TinyTitan/tinytitan.github.io/images/DSC_6004.jpg

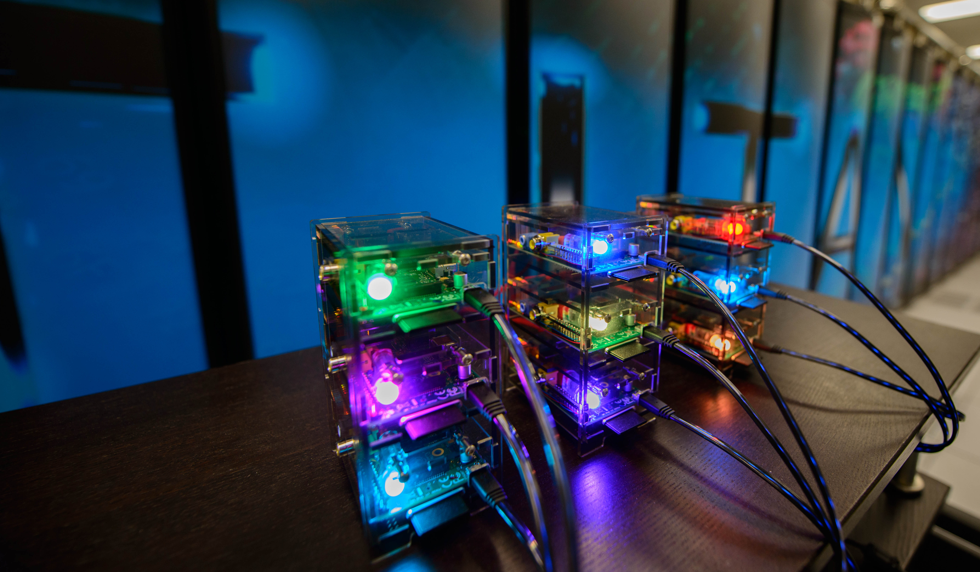
images/DSC_6004.jpg
