TinyTitan/tinytitan.github.io/images/DSC_6060.jpg

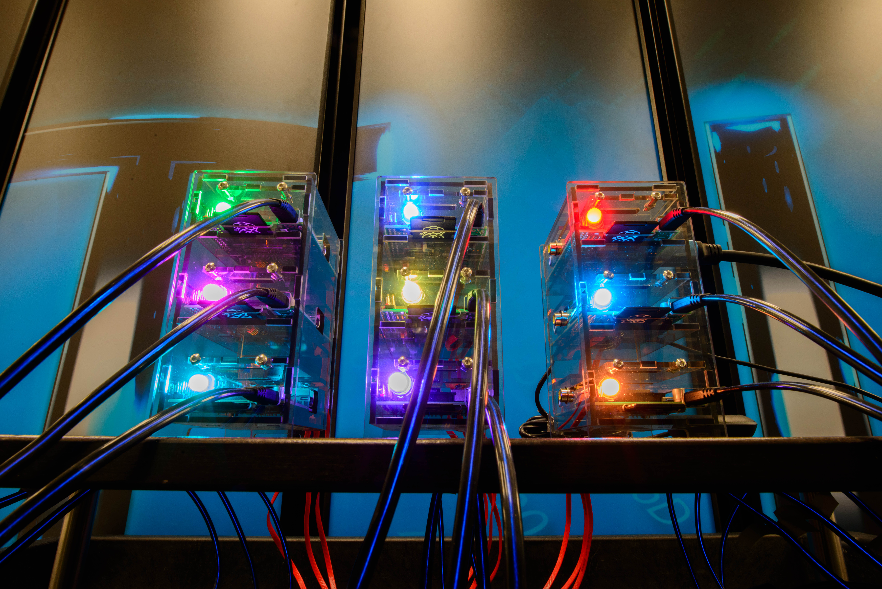
images/DSC_6060.jpg
