TinyTitan/tinytitan.github.io/images/DSC_6062.jpg

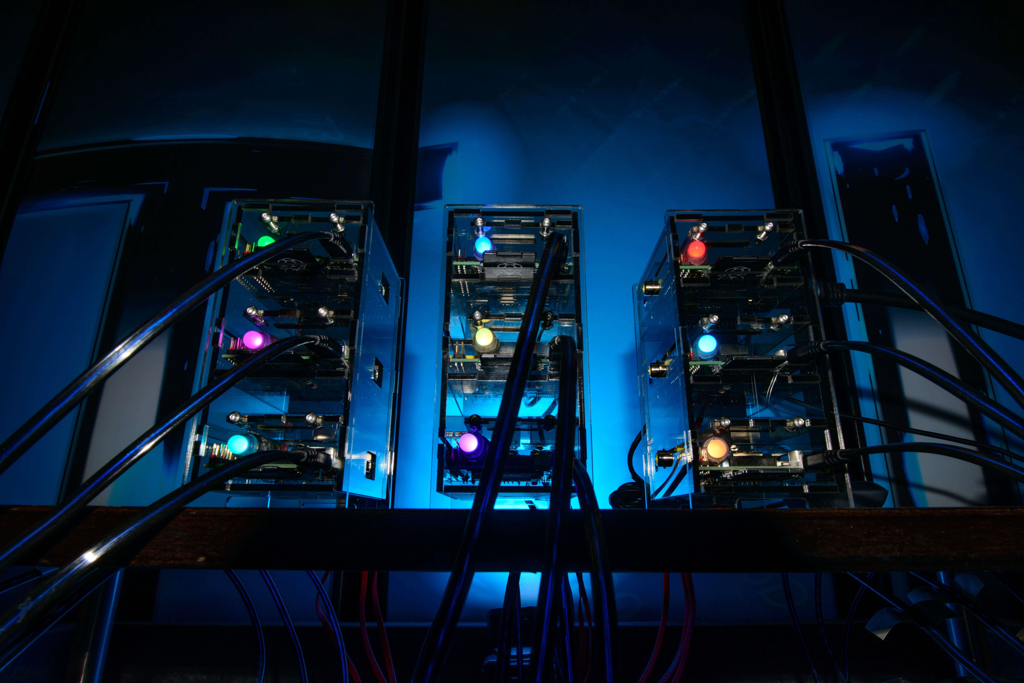
images/DSC_6062.jpg
