TinyTitan/tinytitan.github.io/images/DSC_6087.jpg

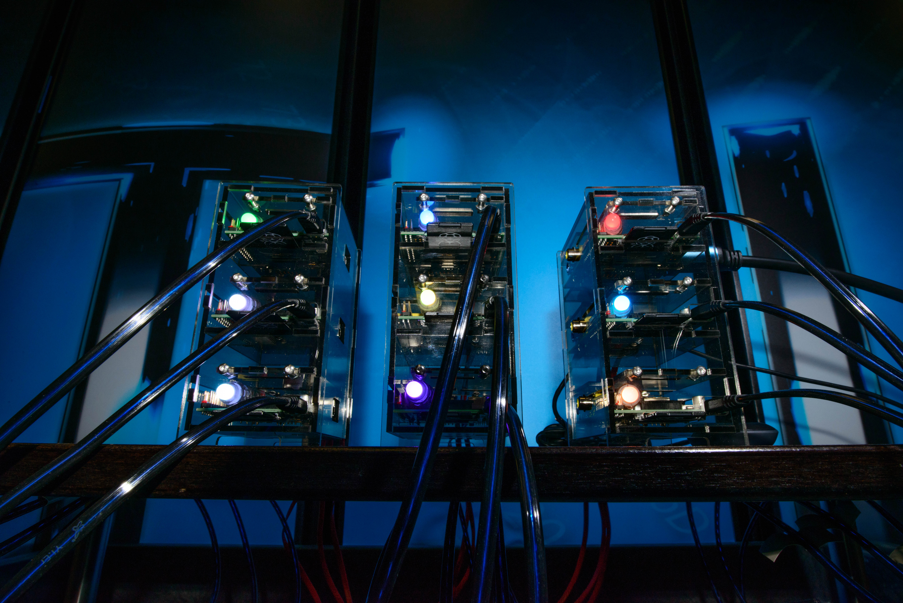
images/DSC_6087.jpg
