TinyTitan/tinytitan.github.io/images/DSC_6102.jpg

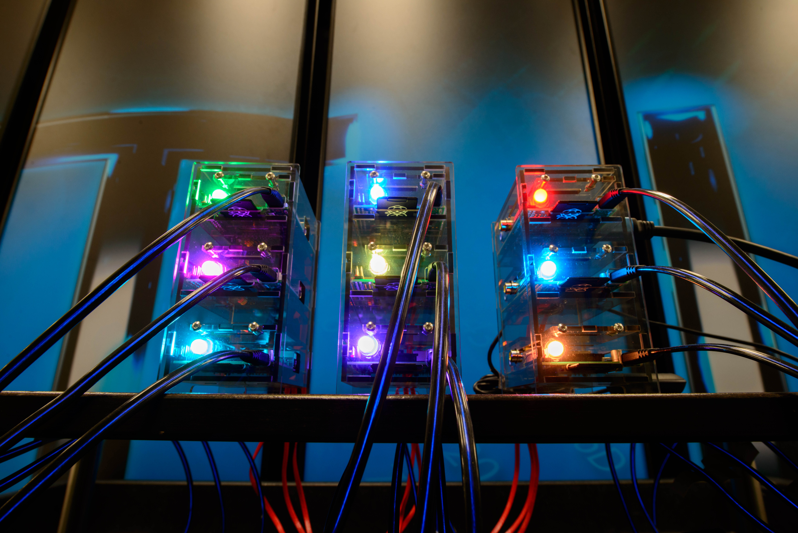
images/DSC_6102.jpg
