TinyTitan/tinytitan.github.io/images/four_cabinet_sph.jpg

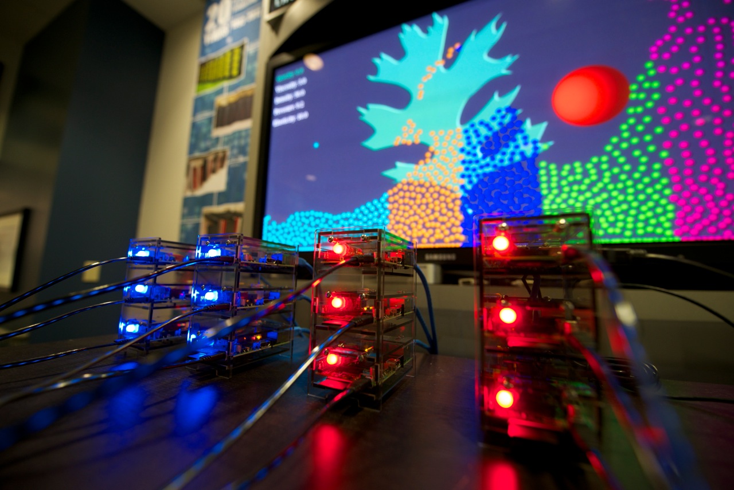
images/four_cabinet_sph.jpg
