TinyTitan/tinytitan.github.io/images/IMG_20140507_095849.jpg

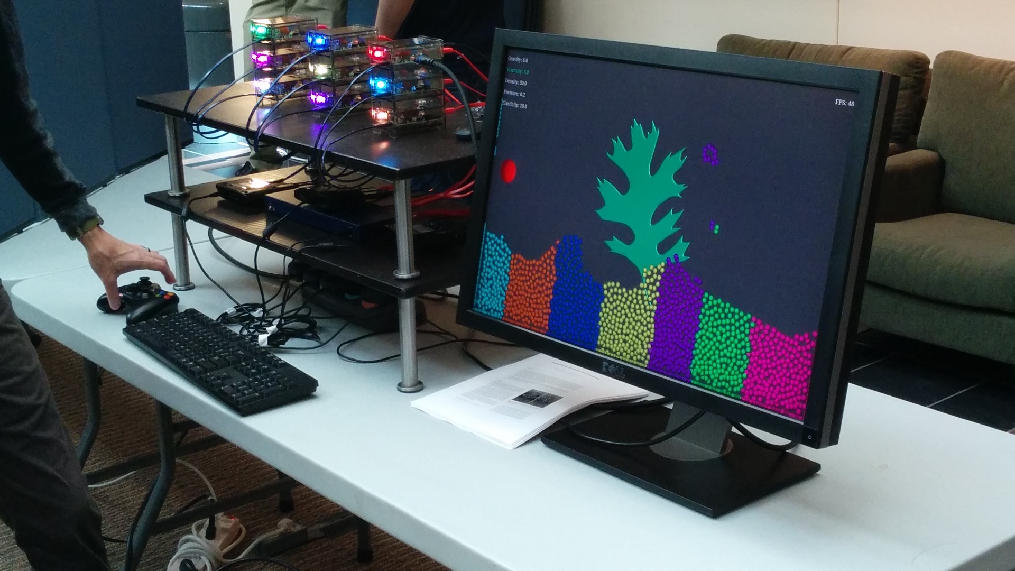
images/IMG_20140507_095849.jpg
