TinyTitan/tinytitan.github.io/images/IMG_20140509_160626.jpg

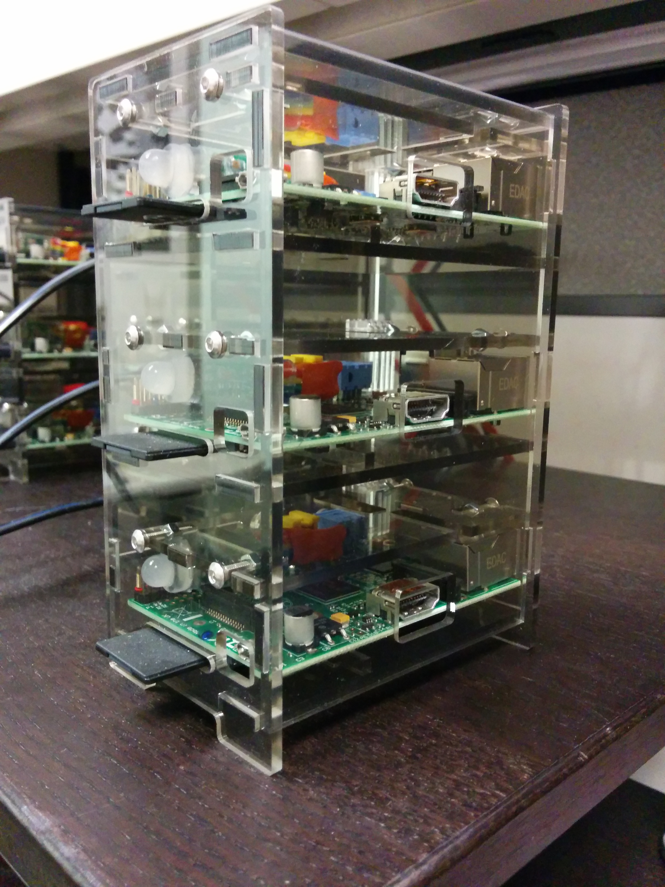
images/IMG_20140509_160626.jpg
