TinyTitan/tinytitan.github.io/images/leaf.png

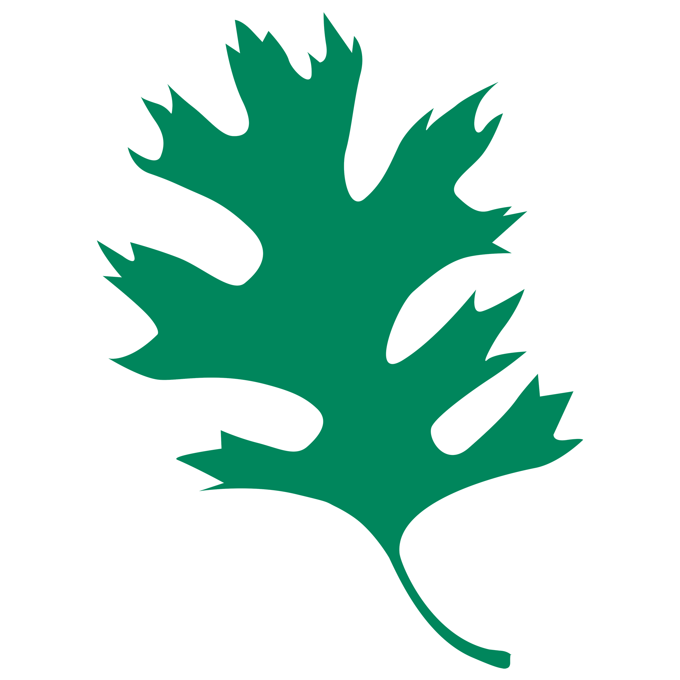
images/leaf.png
