TinyTitan/tinytitan.github.io/images/SPH_Screenshot.png

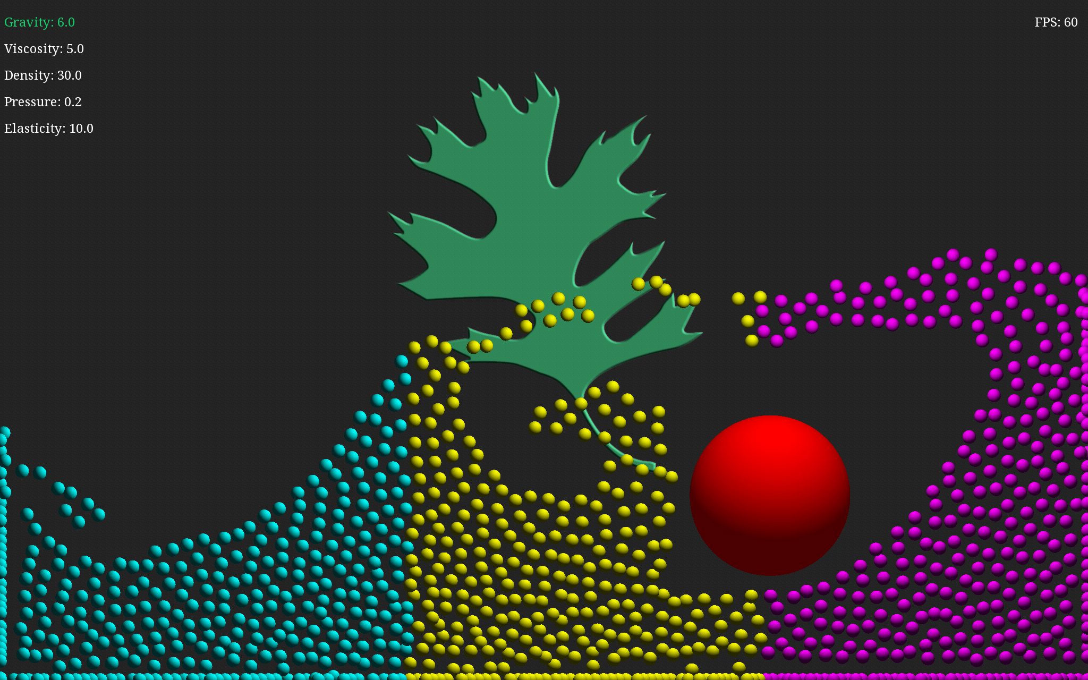
images/SPH_Screenshot.png
