TinyTitan/tinytitan.github.io/images/Construction-v1/image1.jpg

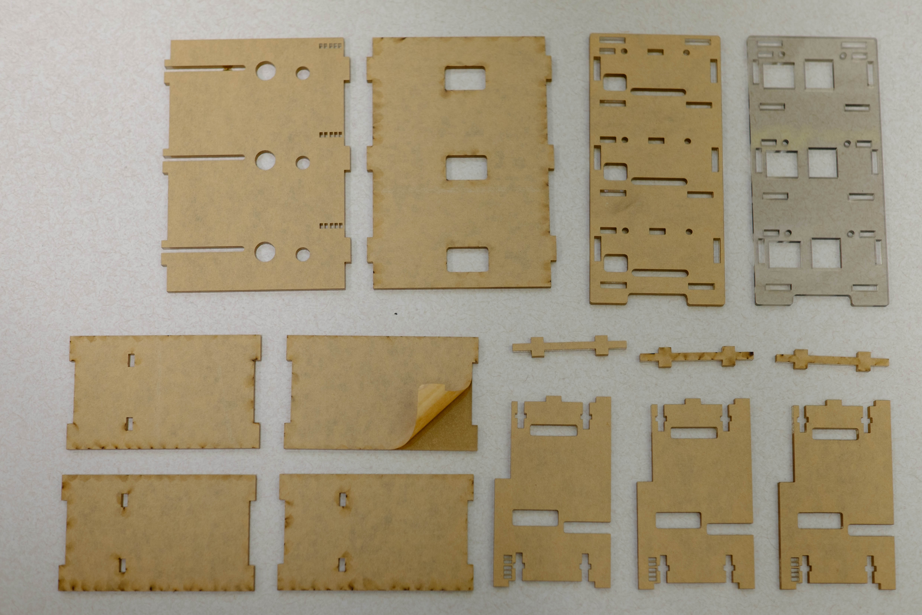
images/Construction-v1/image1.jpg
