TinyTitan/tinytitan.github.io/images/Construction-v1/image2.jpg

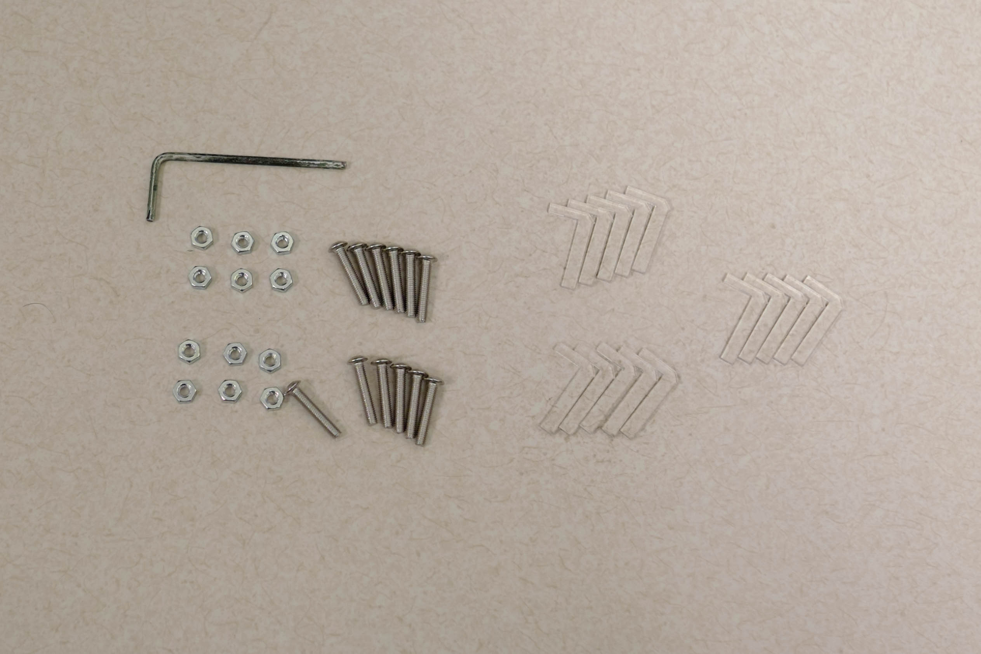
images/Construction-v1/image2.jpg
