TinyTitan/tinytitan.github.io/images/Construction-v1/image3.jpg

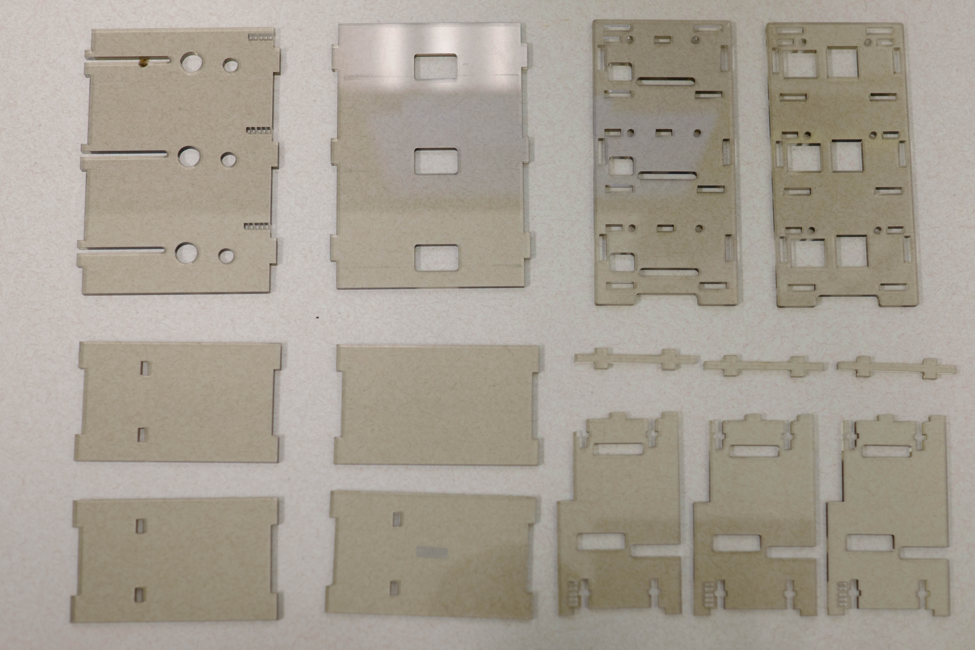
images/Construction-v1/image3.jpg
