TinyTitan/tinytitan.github.io/images/Construction-v1/image4.jpg

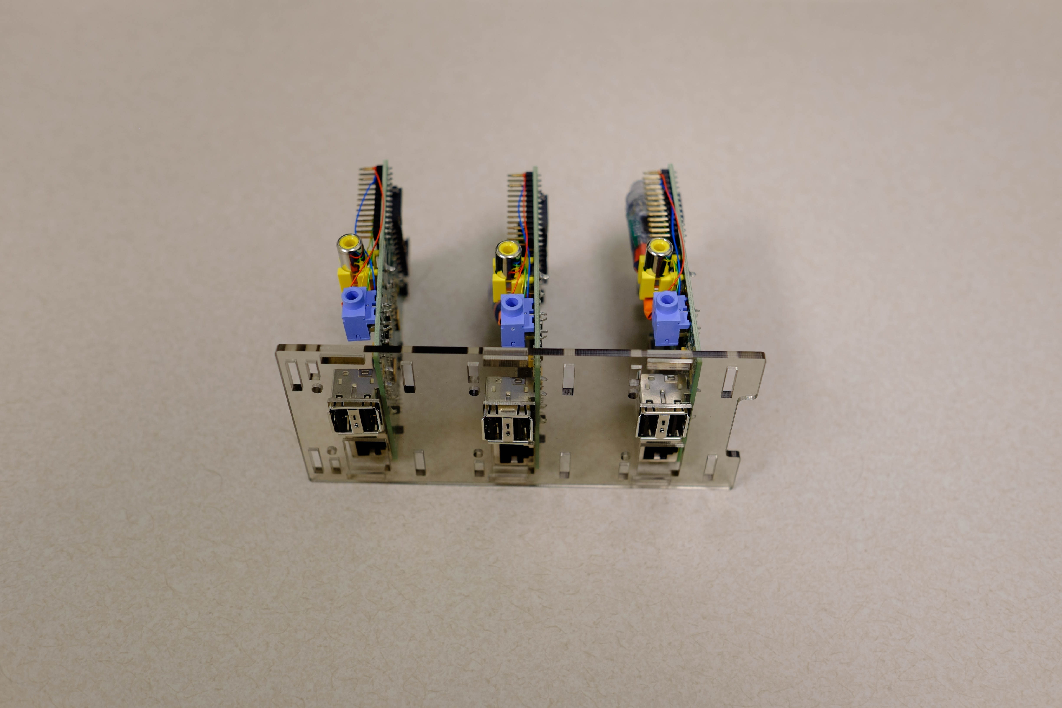
images/Construction-v1/image4.jpg
