TinyTitan/tinytitan.github.io/images/Construction-v1/image6.jpg

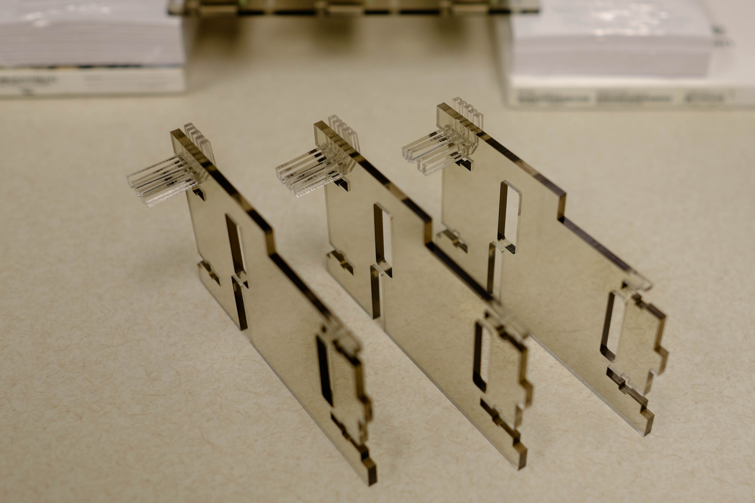
images/Construction-v1/image6.jpg
