TinyTitan/tinytitan.github.io/images/Construction-v1/image7.jpg

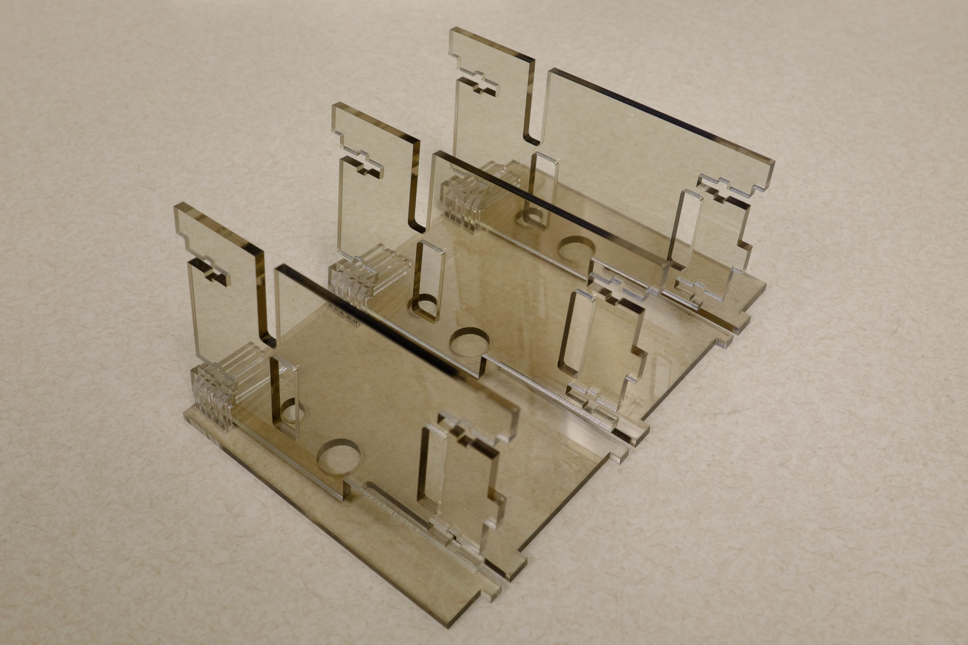
images/Construction-v1/image7.jpg
