TinyTitan/tinytitan.github.io/images/Construction-v1/image8.jpg

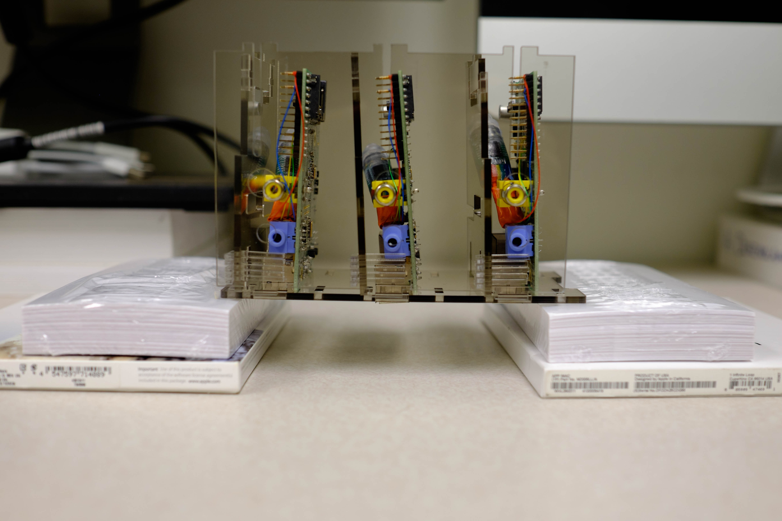
images/Construction-v1/image8.jpg
