TinyTitan/tinytitan.github.io/images/Construction-v1/image10.jpg

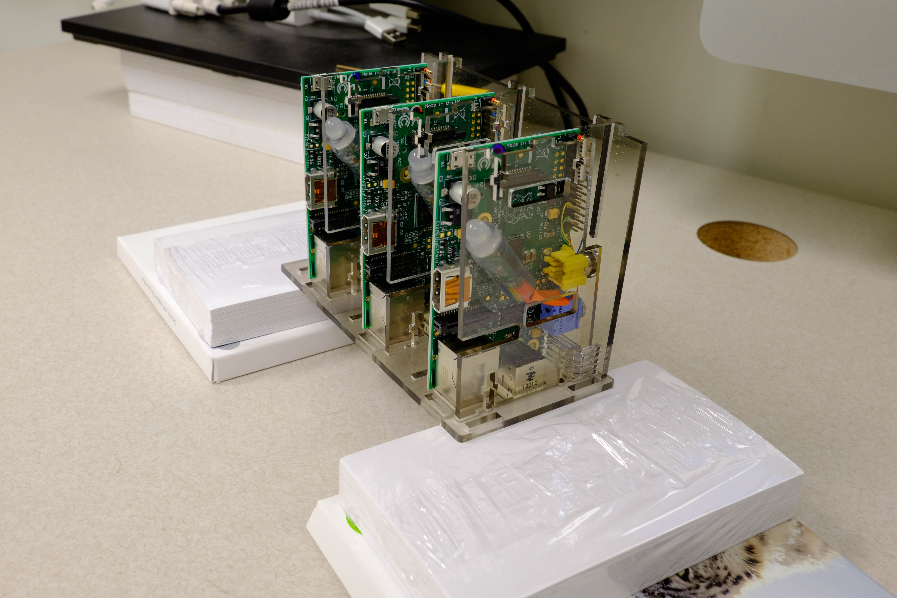
images/Construction-v1/image10.jpg
