TinyTitan/tinytitan.github.io/images/Construction-v1/image12.jpg

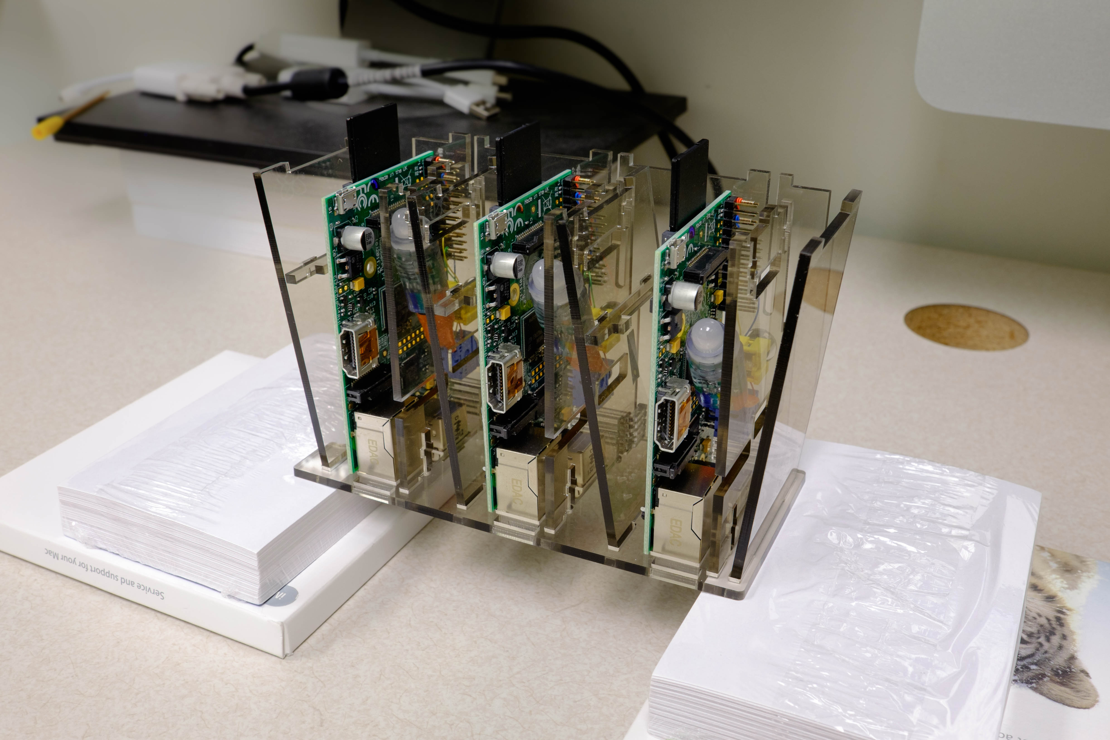
images/Construction-v1/image12.jpg
