TinyTitan/tinytitan.github.io/images/Construction-v1/image13.jpg

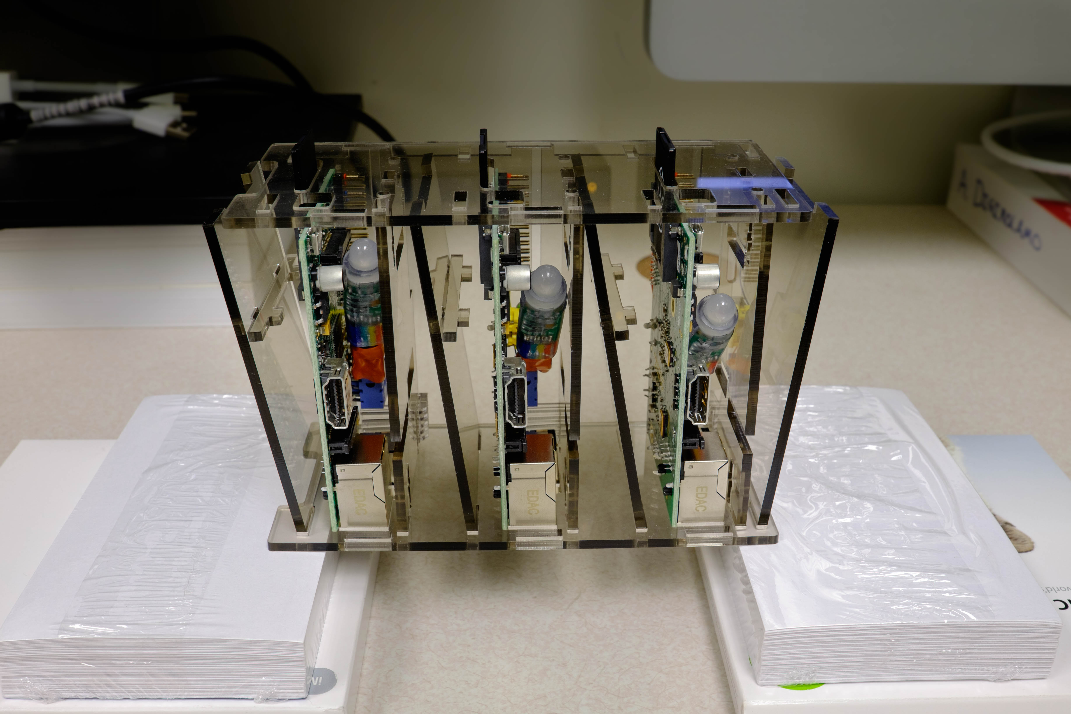
images/Construction-v1/image13.jpg
