TinyTitan/tinytitan.github.io/images/Construction-v1/image14.jpg

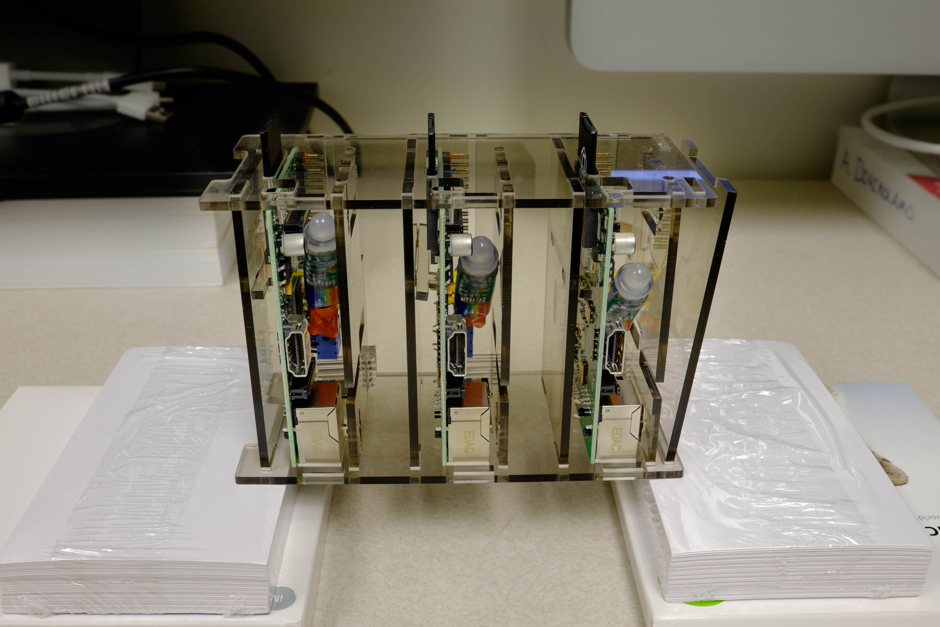
images/Construction-v1/image14.jpg
