TinyTitan/tinytitan.github.io/images/Construction-v1/image16.jpg

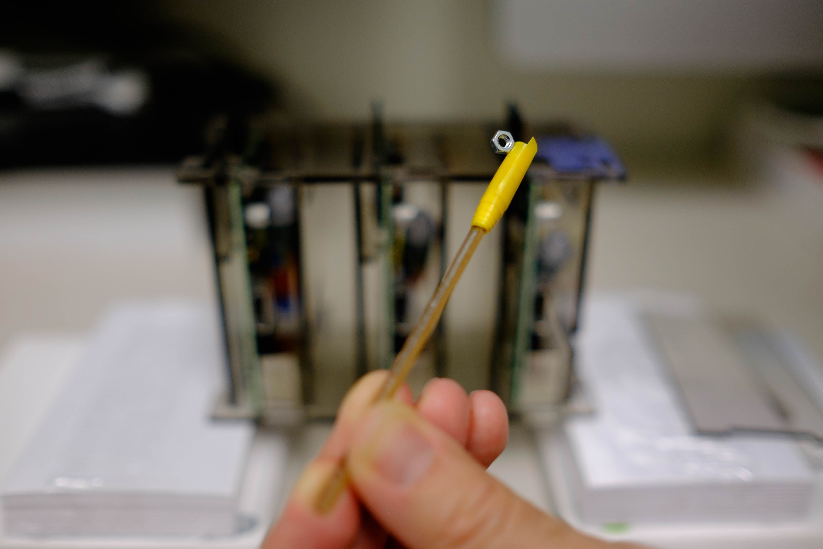
images/Construction-v1/image16.jpg
