TinyTitan/tinytitan.github.io/images/Construction-v1/image18.jpg

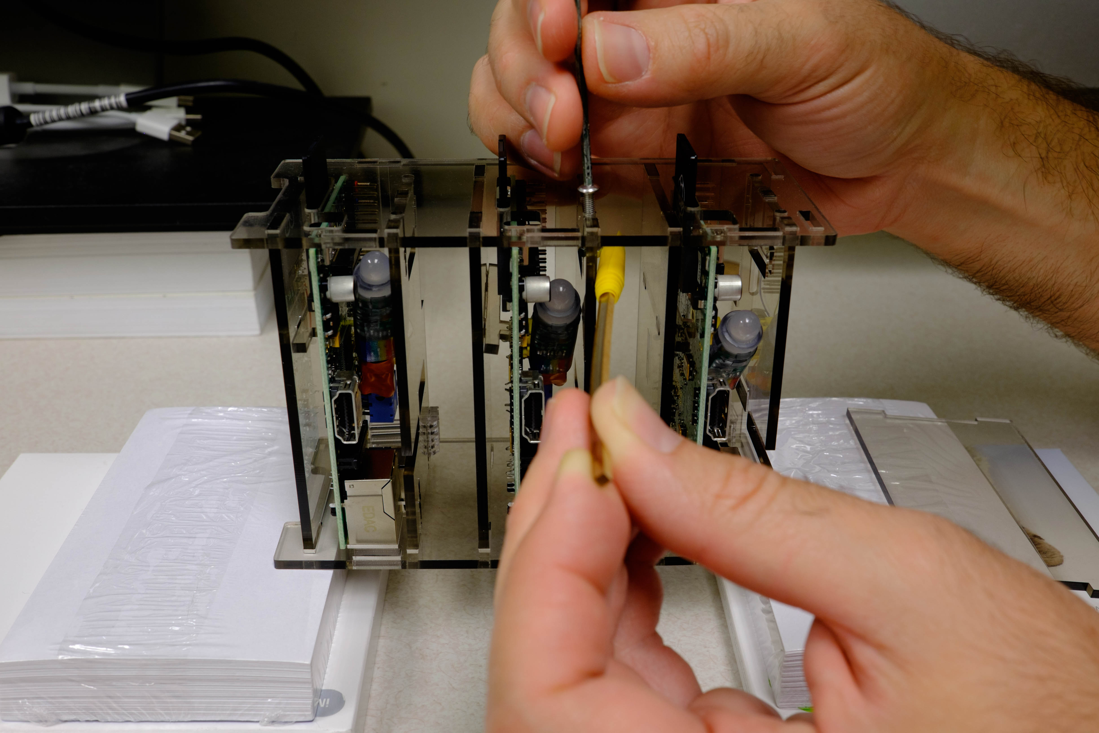
images/Construction-v1/image18.jpg
