TinyTitan/tinytitan.github.io/images/Construction-v1/image19.jpg

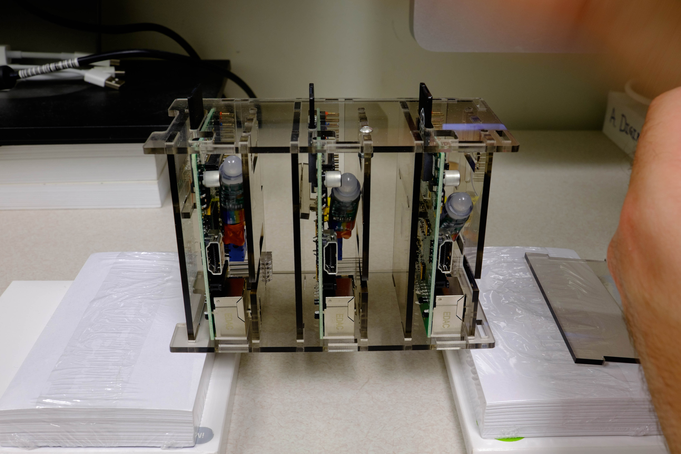
images/Construction-v1/image19.jpg
