TinyTitan/tinytitan.github.io/images/Construction-v1/image20.jpg

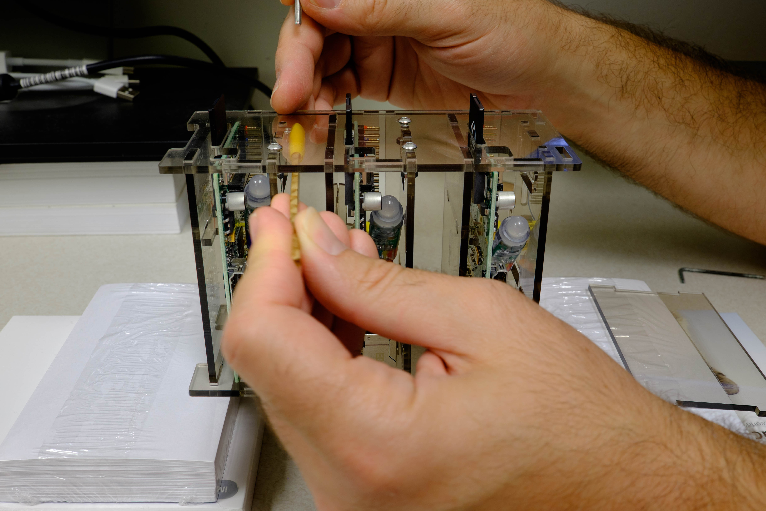
images/Construction-v1/image20.jpg
