TinyTitan/tinytitan.github.io/images/Construction-v1/image21.jpg

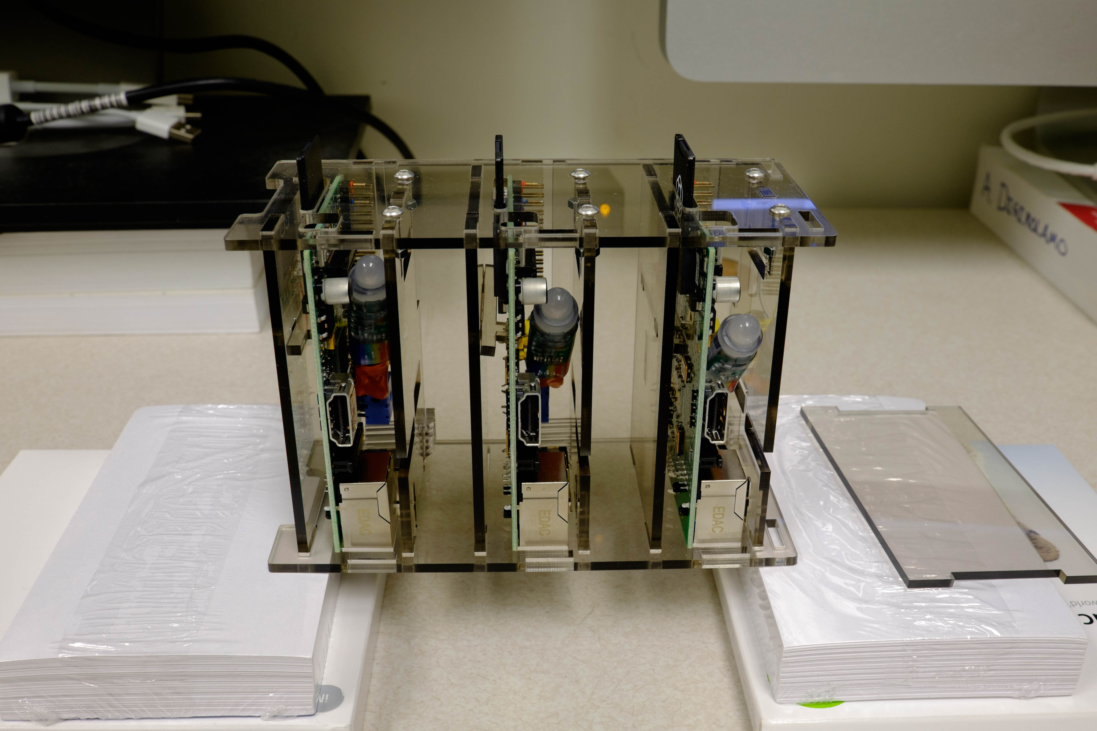
images/Construction-v1/image21.jpg
