TinyTitan/tinytitan.github.io/images/Construction-v1/image22.jpg

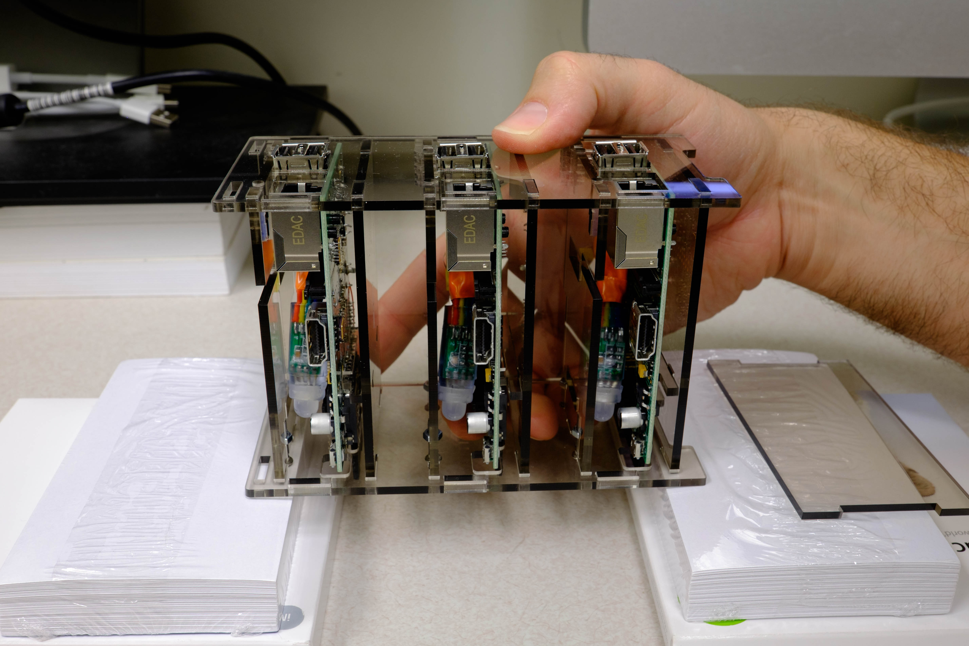
images/Construction-v1/image22.jpg
