TinyTitan/tinytitan.github.io/images/Construction-v1/image23.jpg

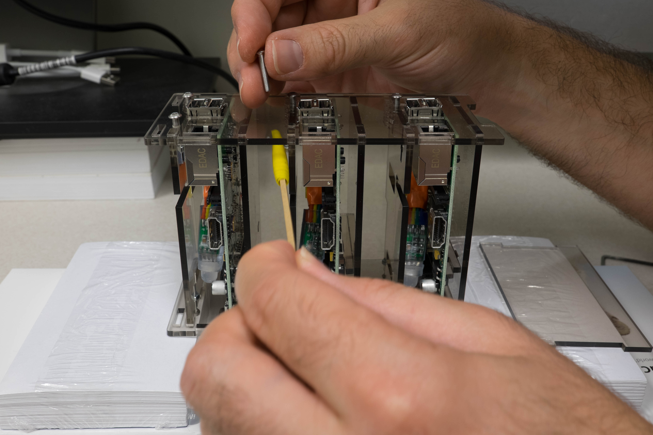
images/Construction-v1/image23.jpg
