TinyTitan/tinytitan.github.io/images/Construction-v1/image24.jpg

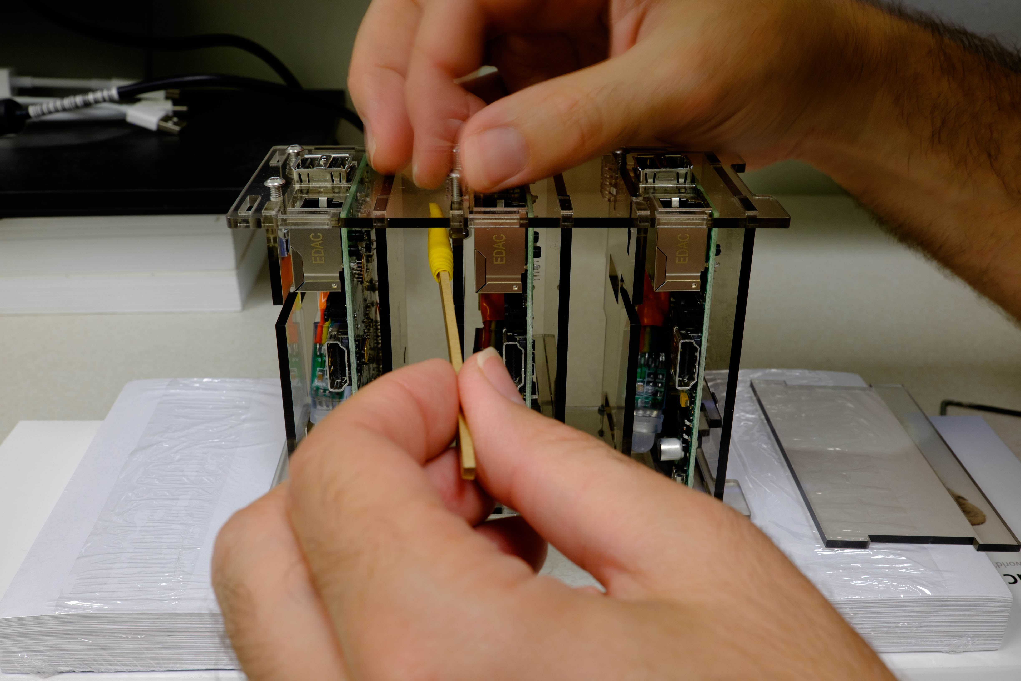
images/Construction-v1/image24.jpg
