TinyTitan/tinytitan.github.io/images/Construction-v1/image27.jpg

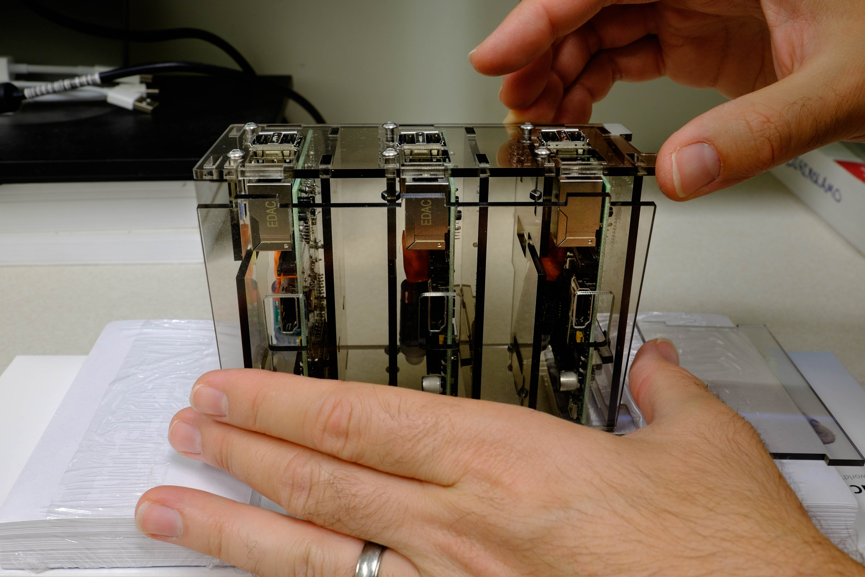
images/Construction-v1/image27.jpg
