TinyTitan/tinytitan.github.io/images/Construction-v1/image28.jpg

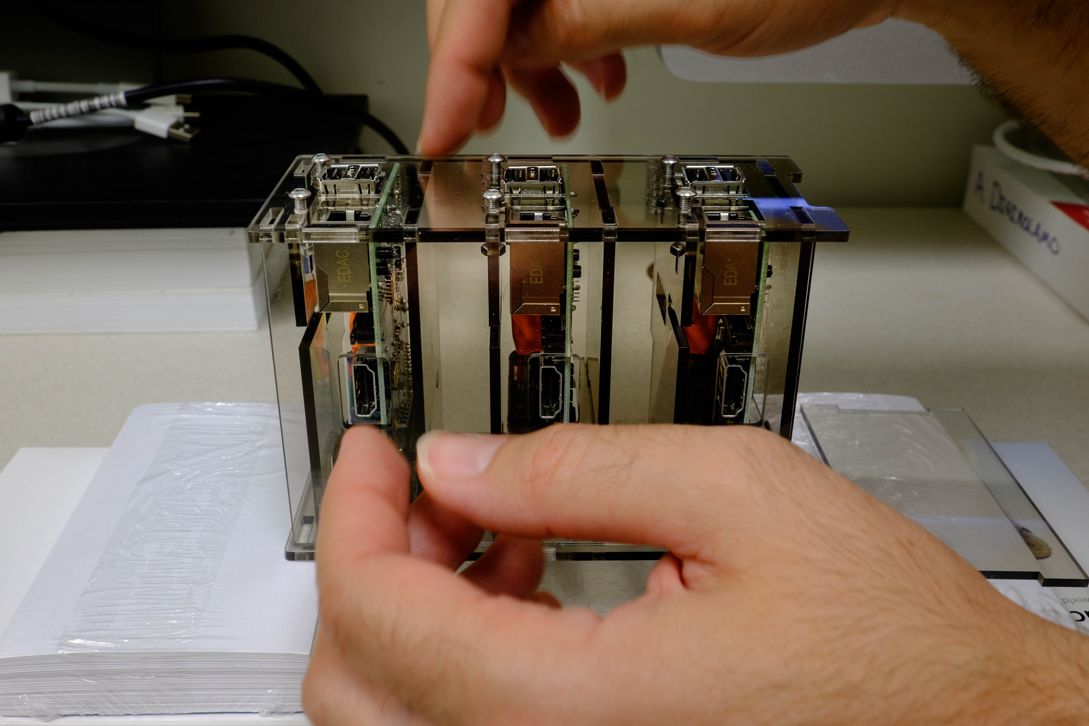
images/Construction-v1/image28.jpg
