TinyTitan/tinytitan.github.io/images/Construction-v1/image29.jpg

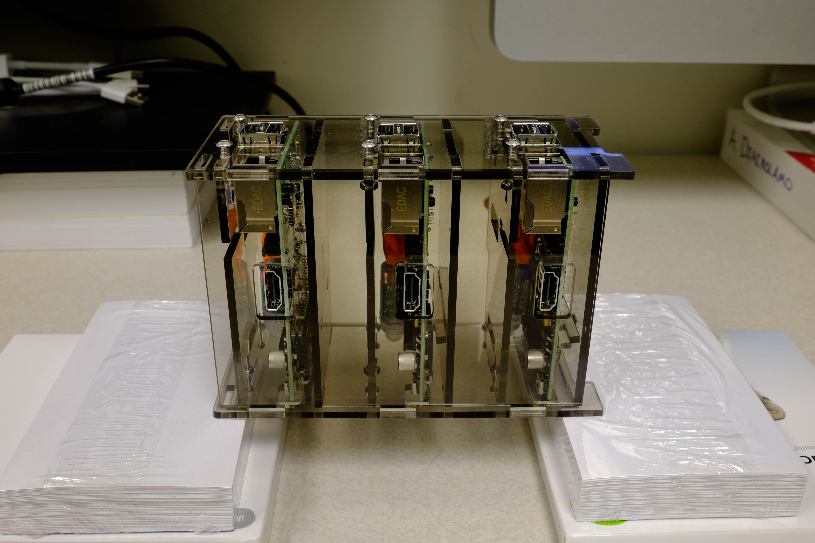
images/Construction-v1/image29.jpg
