TinyTitan/tinytitan.github.io/images/Construction-v1/image30.jpg

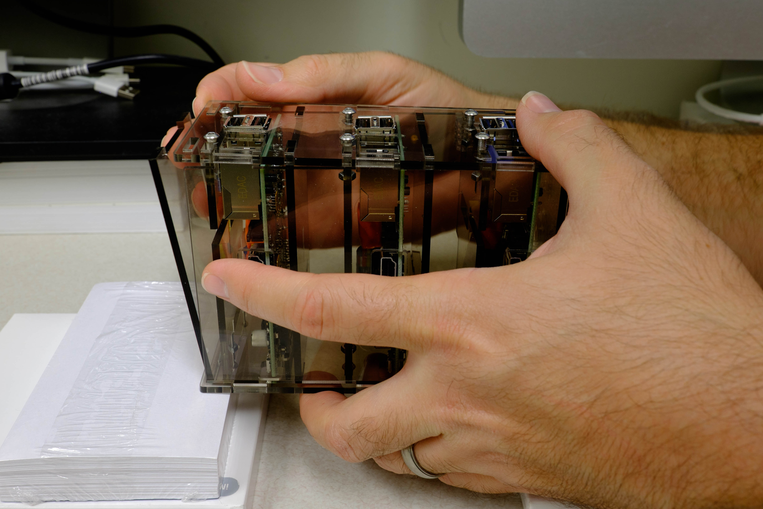
images/Construction-v1/image30.jpg
