TinyTitan/tinytitan.github.io/images/Construction-v1/image31.jpg

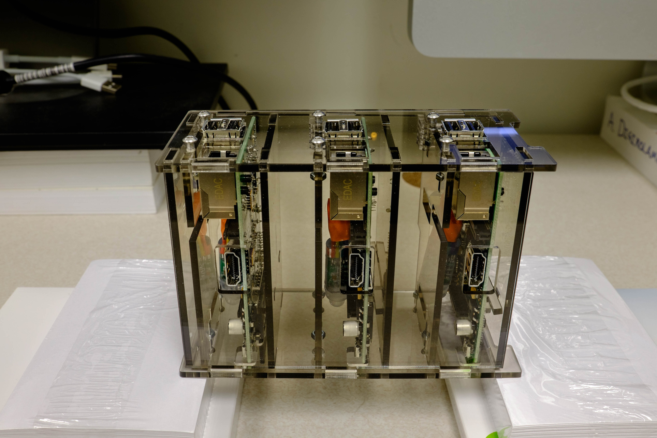
images/Construction-v1/image31.jpg
