TinyTitan/tinytitan.github.io/images/Construction-v1/image32.jpg

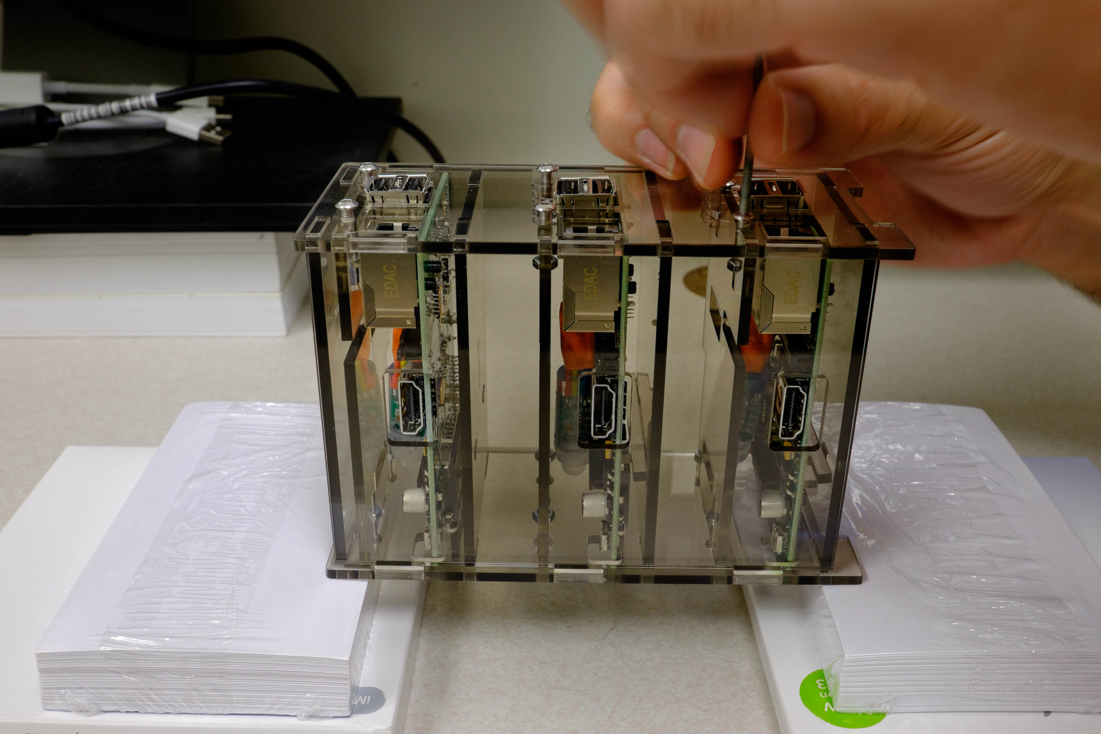
images/Construction-v1/image32.jpg
