TinyTitan/tinytitan.github.io/images/Construction-v1/image33.jpg

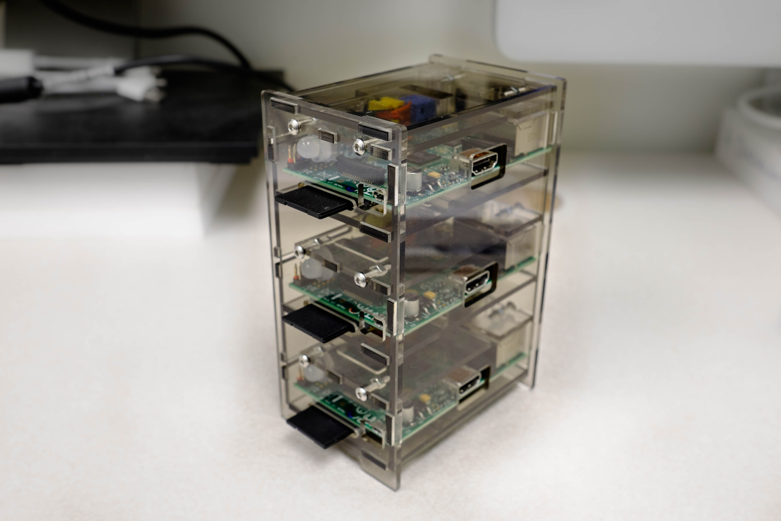
images/Construction-v1/image33.jpg
